mazetrnc/Estacion-Meteorologica/Estación metereológica/prueba_serial_sensoresindiv/bme280/bme280.ino

#include <Wire.h>
#include <Adafruit_Sensor.h>
#include <Adafruit_BME280.h>
#define SDA_PIN 26
#define SCL_PIN 27

#define SEALEVELPRESSURE_HPA (1013.25)

Adafruit_BME280 bme;

void setup() {
  Serial.begin(115200);
  Wire.begin(SDA_PIN, SCL_PIN);
  if (!bme.begin(0x76)) {
    Serial.println("No se encontró un sensor BME280 válido, verifica los cables!");
    while (1);
  } 
}

void loop() {
  Serial.print("Temperatura = ");
  Serial.print(bme.readTemperature());
  Serial.println(" *C");

  Serial.print("Presión = ");
  Serial.print(bme.readPressure() / 100.0F);
  Serial.println(" hPa");

  Serial.print("Altitud aproximada = ");
  Serial.print(bme.readAltitude(SEALEVELPRESSURE_HPA));
  Serial.println(" m");

  Serial.print("Humedad = ");
  Serial.print(bme.readHumidity());
  Serial.println(" %");

  Serial.println();
  delay(1000);
}  
